FioPio/tamtam/board_preview.png

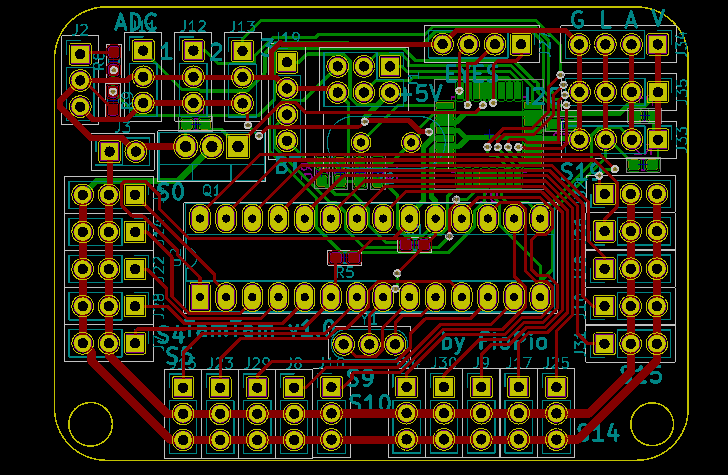
board_preview.png
