FioPio/tamtam/code/rpi/photo_cal/photos/f1.jpg

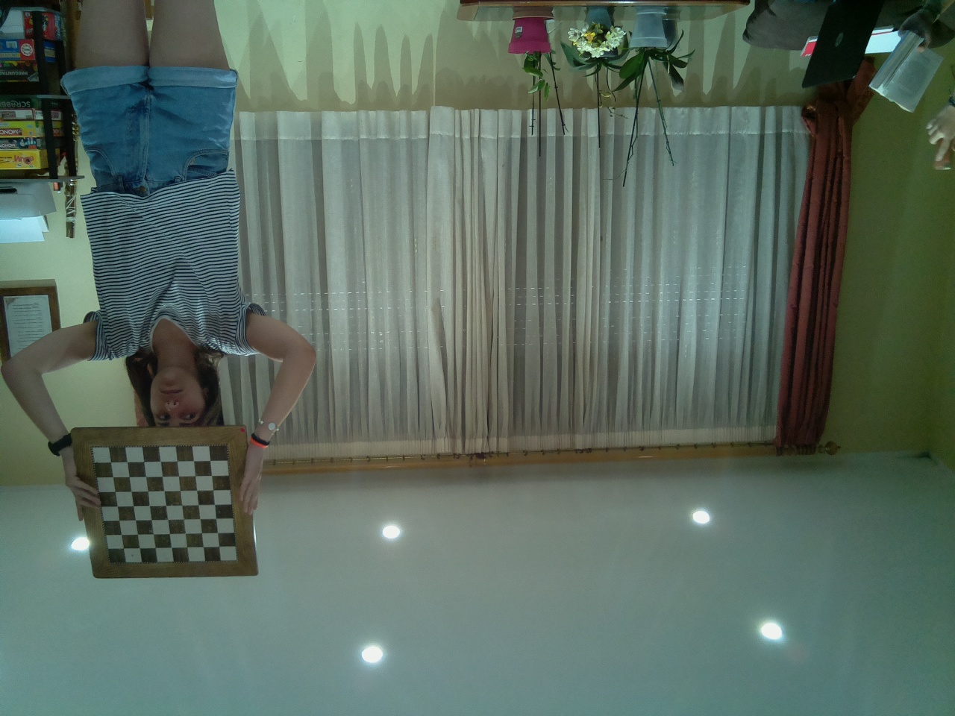
code/rpi/photo_cal/photos/f1.jpg
