FioPio/tamtam/code/rpi/photo_cal/photos/f4.jpg

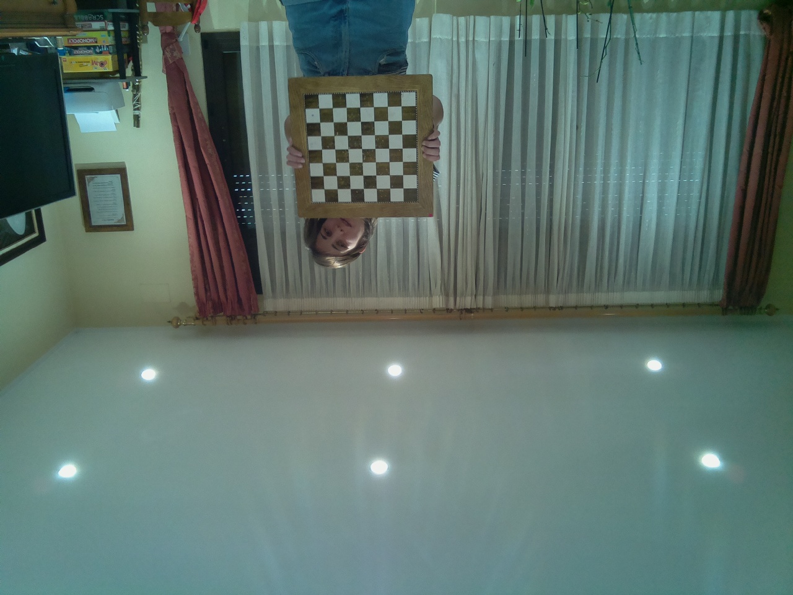
code/rpi/photo_cal/photos/f4.jpg
