FioPio/tamtam/code/rpi/photo_cal/photos/f6.jpg

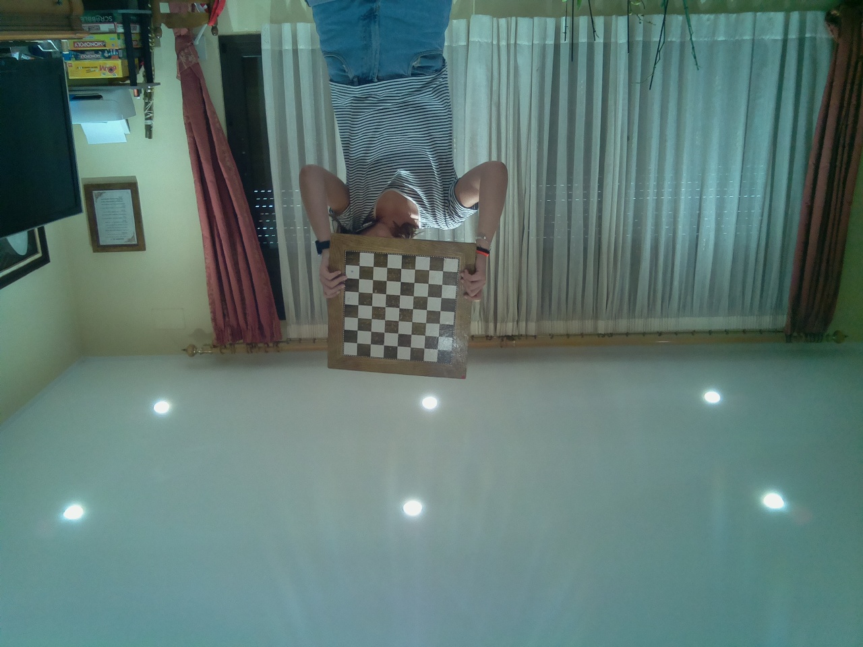
code/rpi/photo_cal/photos/f6.jpg
