FioPio/tamtam/code/rpi/photo_cal/photos/f8.jpg

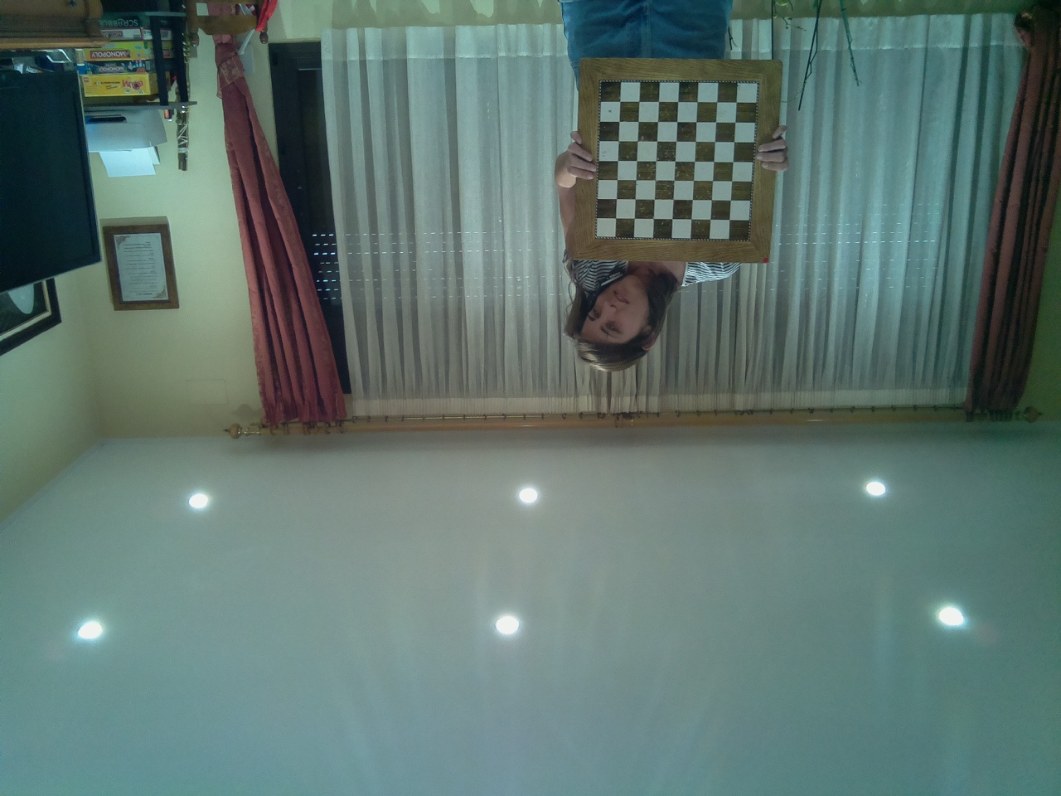
code/rpi/photo_cal/photos/f8.jpg
