FioPio/tamtam/code/rpi/photo_cal/photos/f9.jpg

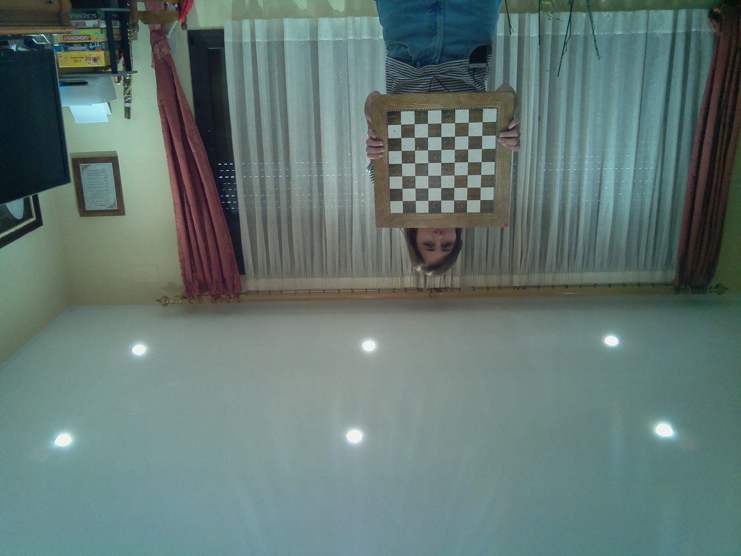
code/rpi/photo_cal/photos/f9.jpg
