FioPio/tamtam/code/rpi/photo_cal/photos/f15.jpg

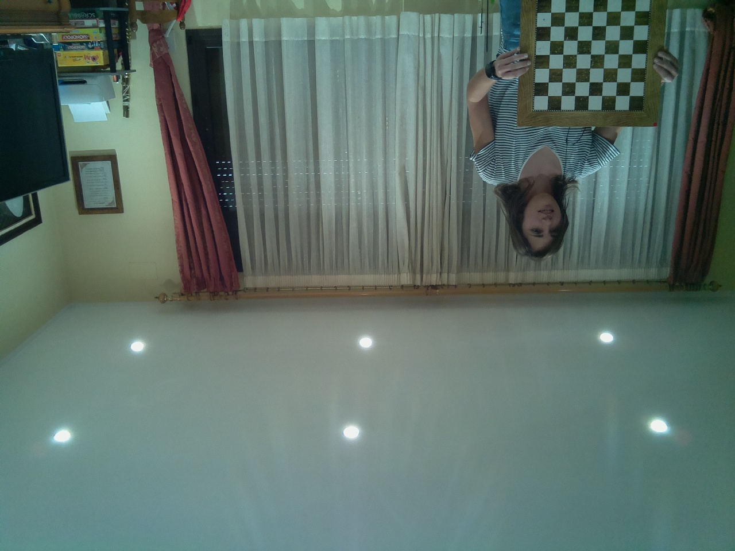
code/rpi/photo_cal/photos/f15.jpg
