FioPio/tamtam/code/rpi/photo_cal/photos/f20.jpg

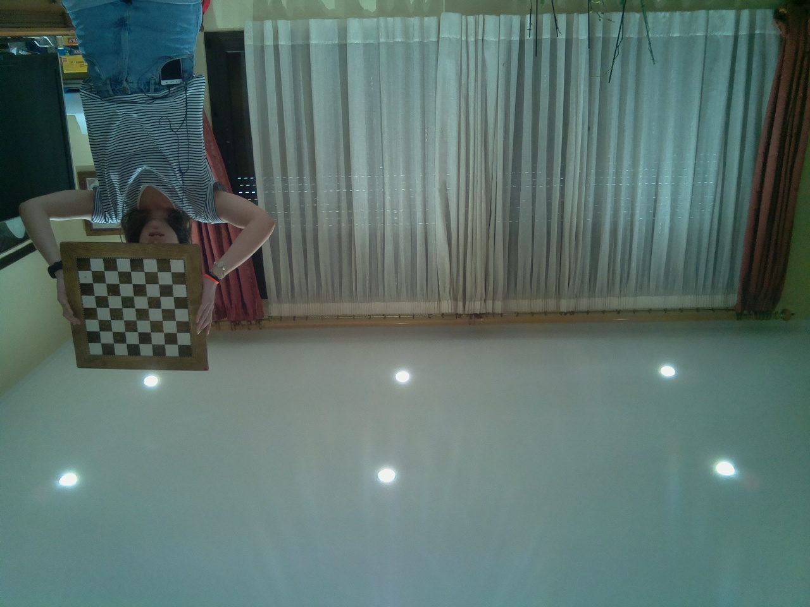
code/rpi/photo_cal/photos/f20.jpg
