FioPio/tamtam/code/rpi/photo_cal/photos/f21.jpg

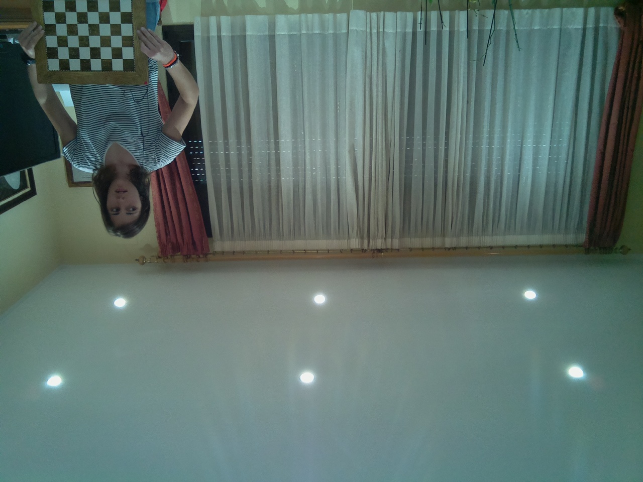
code/rpi/photo_cal/photos/f21.jpg
