FioPio/tamtam/code/rpi/zbar_python/img.jpg

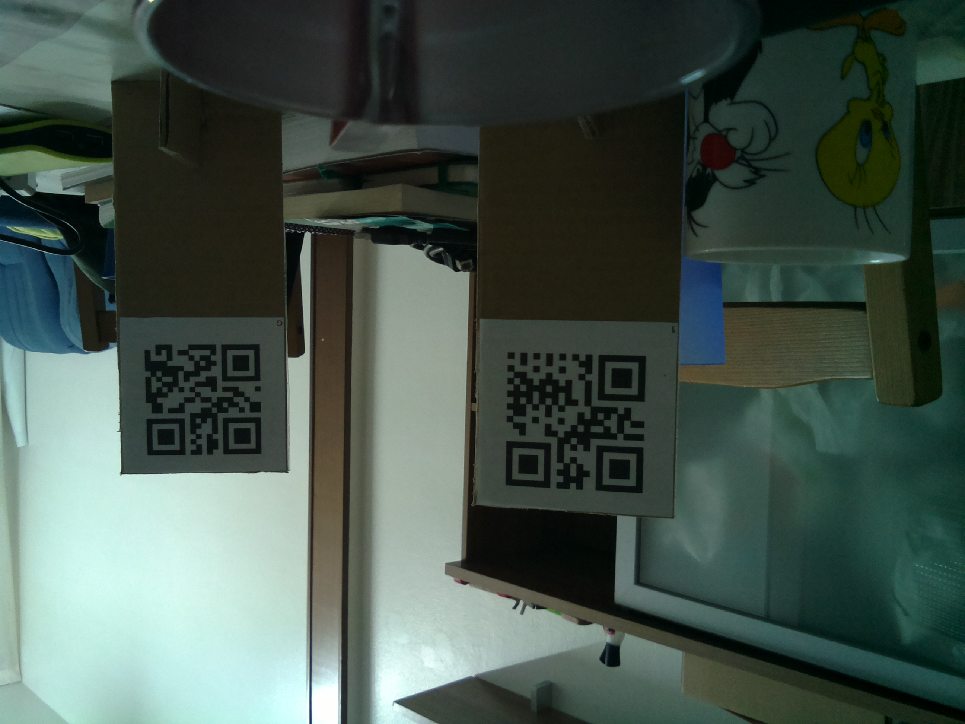
code/rpi/zbar_python/img.jpg
