FioPio/tamtam/markers/1.png

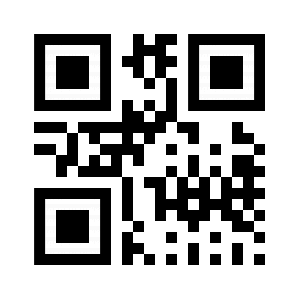
markers/1.png
