FioPio/tamtam/markers/2.png

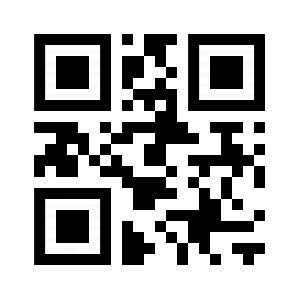
markers/2.png
