FioPio/tamtam/markers/3.png

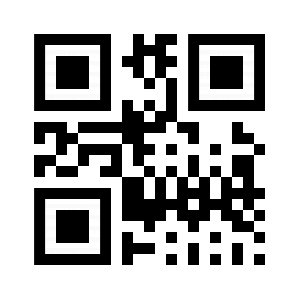
markers/3.png
