FioPio/tamtam/markers/G.png

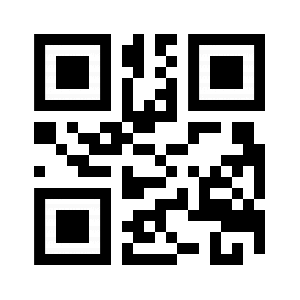
markers/G.png
