FioPio/tamtam/markers/multiple_qr.png

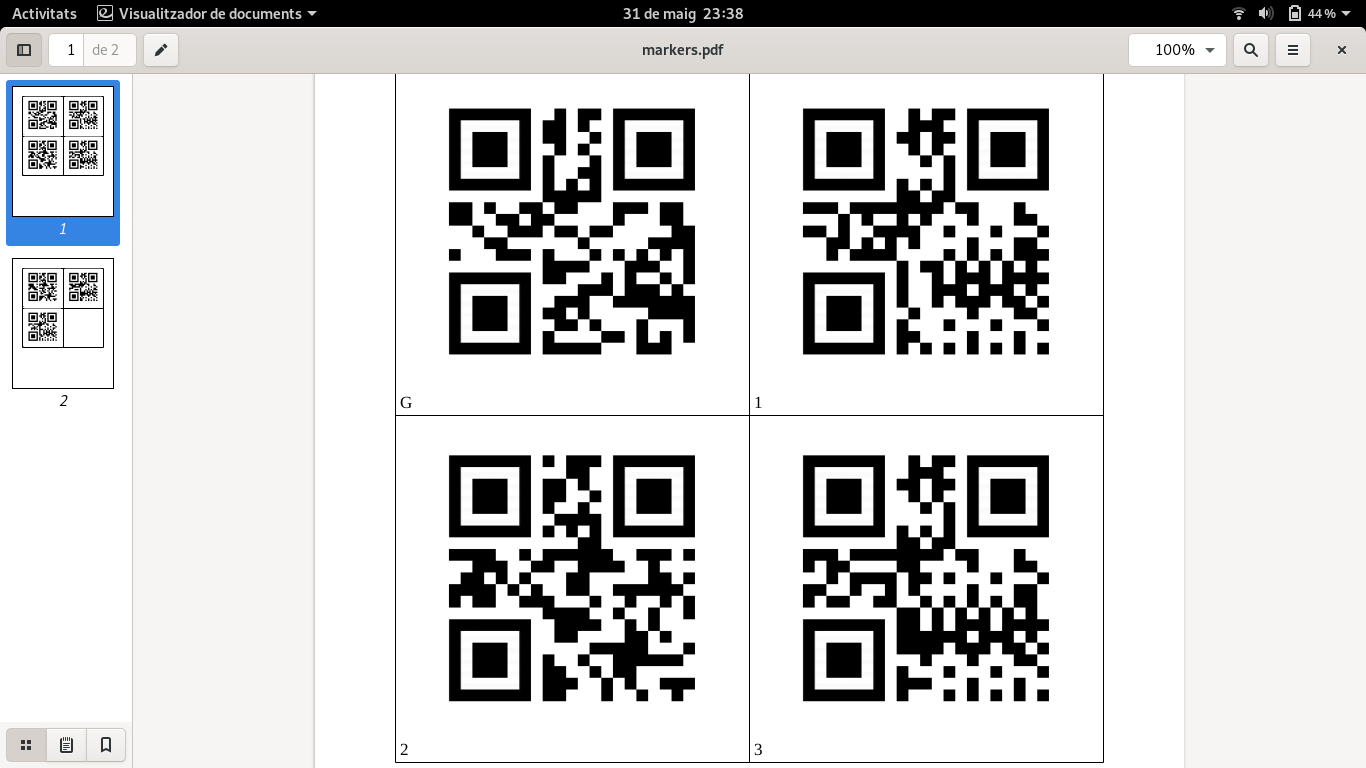
markers/multiple_qr.png
