FioPio/tamtam/TamTam_view2.png

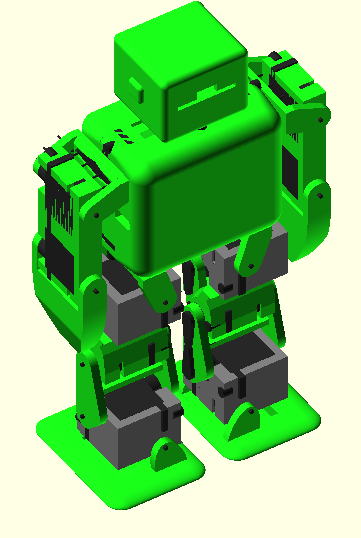
TamTam_view2.png
